ak66666/ThumbsUpUnsplitV2/Silkscreens/Pattern.png

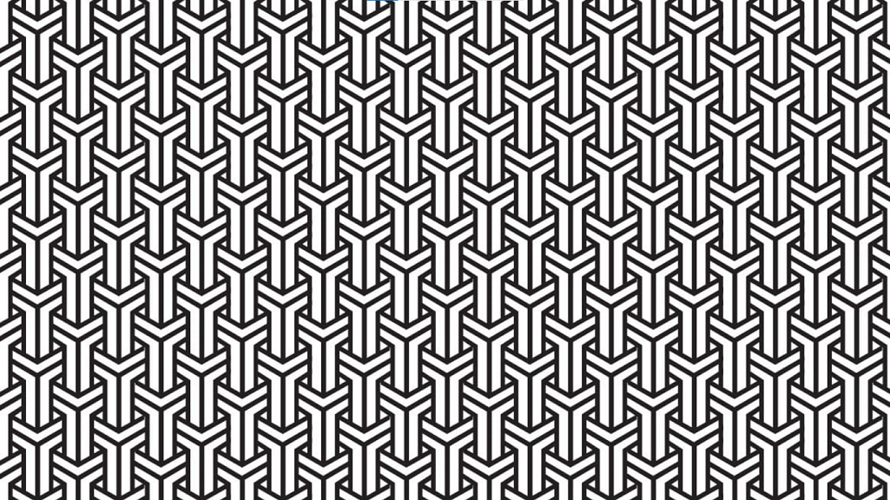
Silkscreens/Pattern.png
