ak66666/ThumbsUpUnsplitV2/Silkscreens/QWERTY.png

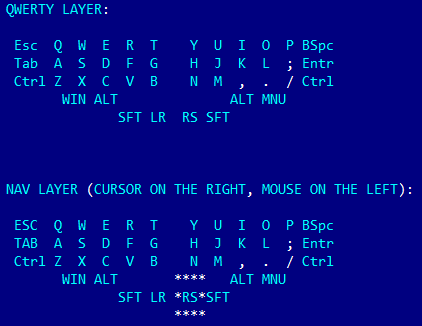
Silkscreens/QWERTY.png
